xCite1986/esp32_t-display-s3-amoled_ph_meter_pump/firmware/ph_dosieranlage_s3/Settings.cpp

#include "Settings.h"
#include <Preferences.h>

Settings settings;

static Preferences prefs;
static const char *NS = "phdos";

static float clampf(float v, float lo, float hi) {
  if (isnan(v)) return lo;
  return v < lo ? lo : (v > hi ? hi : v);
}

void Settings::clampAll() {
  mlPerSec    = clampf(mlPerSec, HARD_MIN_ML_PER_SEC, HARD_MAX_ML_PER_SEC);
  panelDoseMl = clampf(panelDoseMl, 0.1f, HARD_MAX_SINGLE_DOSE_ML);

  if (standbyS < STANDBY_MIN_S) standbyS = STANDBY_MIN_S;
  if (standbyS > STANDBY_MAX_S) standbyS = STANDBY_MAX_S;
  if (shiftS   < SHIFT_MIN_S)   shiftS   = SHIFT_MIN_S;
  if (shiftS   > SHIFT_MAX_S)   shiftS   = SHIFT_MAX_S;
  if (nightFrom > 23) nightFrom = 20;
  if (nightTo   > 23) nightTo   = 5;

  if (circFreshS   < 10)  circFreshS   = 10;
  if (circFreshS   > 3600) circFreshS  = 3600;
  if (circRetryS   < 15)  circRetryS   = 15;
  if (circRetryS   > 3600) circRetryS  = 3600;
  if (circOffRetryS < 15) circOffRetryS = 15;
  if (circOffRetryS > 3600) circOffRetryS = 3600;
  haHost[sizeof(haHost) - 1]     = 0;
  // Ohne Portangabe landet die Anfrage auf Port 80. Dort laeuft haeufig ein
  // anderer Webserver, der mit 404 antwortet - was wie eine falsche Entitaet
  // aussieht. Home Assistant hoert standardmaessig auf 8123, also ergaenzen.
  if (strlen(haHost) > 0 && strchr(haHost, ':') == nullptr &&
      strlen(haHost) + 5 < sizeof(haHost)) {
    strcat(haHost, ":8123");
  }
  haToken[sizeof(haToken) - 1]   = 0;
  haEntity[sizeof(haEntity) - 1] = 0;
  haOnState[sizeof(haOnState) - 1] = 0;
  if (strlen(haOnState) == 0) strcpy(haOnState, "on");
  // Ohne Adresse, Entitaet oder Token laesst sich nichts pruefen - dann bleibt
  // die Verriegelung aus, statt jede Dosierung zu blockieren.
  if (strlen(haHost) == 0 || strlen(haEntity) == 0 || strlen(haToken) == 0)
    circEnabled = false;

  phSetpoint  = clampf(phSetpoint, 6.0f, 8.5f);
  phDeadband  = clampf(phDeadband, 0.01f, 1.0f);
  phMinLock   = clampf(phMinLock, HARD_MIN_PH_LOCK, 7.5f);
  phMaxPlaus  = clampf(phMaxPlaus, 8.0f, PH_PLAUS_MAX);

  maxSingleMl = clampf(maxSingleMl, 0.1f, HARD_MAX_SINGLE_DOSE_ML);
  doseMl      = clampf(doseMl, 0.1f, maxSingleMl);
  maxDailyMl  = clampf(maxDailyMl, 0.1f, HARD_MAX_DAILY_ML);
  if (pauseS < HARD_MIN_PAUSE_S) pauseS = HARD_MIN_PAUSE_S;
  if (pauseS > 86400UL) pauseS = 86400UL;

  if (adcGain > (uint8_t)ADS_GAIN_0256) adcGain = (uint8_t)ADS_GAIN_4096;
  if (filterS < PH_FILTER_MIN_S) filterS = PH_FILTER_MIN_S;
  if (filterS > PH_FILTER_MAX_S) filterS = PH_FILTER_MAX_S;
  if (phAvgS  < PH_AVG_MIN_S)    phAvgS  = PH_AVG_MIN_S;
  if (phAvgS  > PH_AVG_MAX_S)    phAvgS  = PH_AVG_MAX_S;
  phStableBand = clampf(phStableBand, PH_STABLE_BAND_MIN, PH_STABLE_BAND_MAX);

  calPhA = clampf(calPhA, 0.0f, 14.0f);
  calPhB = clampf(calPhB, 0.0f, 14.0f);
  calVoltA = clampf(calVoltA, -6.2f, 6.2f);
  calVoltB = clampf(calVoltB, -6.2f, 6.2f);
  // Zwei Kalibrierpunkte muessen sich unterscheiden, sonst ist die Gerade sinnlos.
  if (fabsf(calPhA - calPhB) < 0.5f || fabsf(calVoltA - calVoltB) < 0.010f) {
    calValid = false;
  }

  dailyMl = clampf(dailyMl, 0.0f, HARD_MAX_DAILY_ML);
  if (totalMl < 0) totalMl = 0;

  hostname[sizeof(hostname) - 1] = 0;
  wifiSsid[sizeof(wifiSsid) - 1] = 0;
  wifiPass[sizeof(wifiPass) - 1] = 0;
  webUser[sizeof(webUser) - 1]   = 0;
  webPass[sizeof(webPass) - 1]   = 0;
}

static void getStr(Preferences &p, const char *key, char *dst, size_t len, const char *def) {
  String s = p.getString(key, def);
  strncpy(dst, s.c_str(), len - 1);
  dst[len - 1] = 0;
}

void Settings::load() {
  prefs.begin(NS, true);  // read-only

  getStr(prefs, "ssid", wifiSsid, sizeof(wifiSsid), "");
  getStr(prefs, "pass", wifiPass, sizeof(wifiPass), "");
  getStr(prefs, "host", hostname, sizeof(hostname), "ph-dosierung");
  getStr(prefs, "wuser", webUser, sizeof(webUser), "");
  getStr(prefs, "wpass", webPass, sizeof(webPass), "");

  calValid   = prefs.getBool("calok", false);
  calPhA     = prefs.getFloat("cpha", 7.00f);
  calVoltA   = prefs.getFloat("cva", 1.65f);
  calPhB     = prefs.getFloat("cphb", 4.00f);
  calVoltB   = prefs.getFloat("cvb", 2.00f);
  adcGain    = prefs.getUChar("gain", (uint8_t)ADS_GAIN_4096);
  filterS    = (uint16_t)prefs.getULong("filt", 30);
  phAvgS     = (uint16_t)prefs.getULong("avgs", 600);
  phStableBand = prefs.getFloat("stbnd", PH_STABLE_BAND);

  mlPerSec   = prefs.getFloat("mlps", DEFAULT_ML_PER_SEC);
  panelDoseMl= prefs.getFloat("pdose", DEFAULT_PANEL_DOSE_ML);
  relayInvert= prefs.getBool("rinv", false);
  standbyS   = (uint16_t)prefs.getULong("stby", 300);
  shiftS     = (uint16_t)prefs.getULong("shft", 300);
  nightEnabled = prefs.getBool("nite", true);
  rot180     = prefs.getBool("rot180", true);
  nightFrom  = prefs.getUChar("nfrom", 20);
  nightTo    = prefs.getUChar("nto", 5);

  circEnabled = prefs.getBool("circen", false);
  getStr(prefs, "hahost", haHost, sizeof(haHost), "");
  getStr(prefs, "hatok", haToken, sizeof(haToken), "");
  getStr(prefs, "haent", haEntity, sizeof(haEntity), "switch.poolpumpe");
  getStr(prefs, "haon", haOnState, sizeof(haOnState), "on");
  circFreshS  = (uint16_t)prefs.getULong("circfr", 120);
  circRetryS  = (uint16_t)prefs.getULong("circrt", 60);
  circOffRetryS = (uint16_t)prefs.getULong("circof", 120);

  autoEnabled= prefs.getBool("auto", false);
  phSetpoint = prefs.getFloat("sp", 7.20f);
  phDeadband = prefs.getFloat("db", 0.05f);
  doseMl     = prefs.getFloat("dose", 3.00f);
  maxSingleMl= prefs.getFloat("maxs", 5.00f);
  maxDailyMl = prefs.getFloat("maxd", 60.00f);
  pauseS     = prefs.getULong("pause", 1800);
  phMinLock  = prefs.getFloat("phlock", 6.80f);
  phMaxPlaus = prefs.getFloat("phmax", 9.50f);


  dailyMl    = prefs.getFloat("dml", 0.0f);
  dayStamp   = prefs.getULong("dstamp", 0);
  totalMl    = prefs.getFloat("tml", 0.0f);

  prefs.end();
  clampAll();
}

// 95 Prozent der Vollskala: die letzten Prozent gehoeren der Stoerung, die
// auf dem Nutzsignal sitzt. Wird die Spitze abgeschnitten, stimmt auch der
// netzsynchrone Mittelwert nicht mehr.
bool Settings::gainFitsCalibration(uint8_t gainIdx, String &err) const {
  if (gainIdx > (uint8_t)ADS_GAIN_0256) { err = "unbekannter Messbereich"; return false; }
  if (!calValid) return true;                 // ohne Kalibrierung nichts zu pruefen

  float fs   = Ads1115::fullScaleOf((AdsGain)gainIdx) * 0.95f;
  float vmax = fabsf(calVoltA) > fabsf(calVoltB) ? fabsf(calVoltA) : fabsf(calVoltB);
  if (vmax <= fs) return true;

  err  = "Messbereich zu klein: Kalibrierpunkt ";
  err += String(vmax, 3);
  err += " V passt nicht in +/-";
  err += String(Ads1115::fullScaleOf((AdsGain)gainIdx), 3);
  err += " V. Erst Kalibrierung verwerfen, dann umstellen.";
  return false;
}

void Settings::save() {
  clampAll();
  prefs.begin(NS, false);

  prefs.putString("ssid", wifiSsid);
  prefs.putString("pass", wifiPass);
  prefs.putString("host", hostname);
  prefs.putString("wuser", webUser);
  prefs.putString("wpass", webPass);

  prefs.putBool("calok", calValid);
  prefs.putFloat("cpha", calPhA);
  prefs.putFloat("cva", calVoltA);
  prefs.putFloat("cphb", calPhB);
  prefs.putFloat("cvb", calVoltB);
  prefs.putUChar("gain", adcGain);
  prefs.putULong("filt", filterS);
  prefs.putULong("avgs", phAvgS);
  prefs.putFloat("stbnd", phStableBand);

  prefs.putFloat("mlps", mlPerSec);
  prefs.putFloat("pdose", panelDoseMl);
  prefs.putBool("rinv", relayInvert);
  prefs.putULong("stby", standbyS);
  prefs.putULong("shft", shiftS);
  prefs.putBool("nite", nightEnabled);
  prefs.putBool("rot180", rot180);
  prefs.putUChar("nfrom", nightFrom);
  prefs.putUChar("nto", nightTo);

  prefs.putBool("circen", circEnabled);
  prefs.putString("hahost", haHost);
  prefs.putString("hatok", haToken);
  prefs.putString("haent", haEntity);
  prefs.putString("haon", haOnState);
  prefs.putULong("circfr", circFreshS);
  prefs.putULong("circrt", circRetryS);
  prefs.putULong("circof", circOffRetryS);

  prefs.putBool("auto", autoEnabled);
  prefs.putFloat("sp", phSetpoint);
  prefs.putFloat("db", phDeadband);
  prefs.putFloat("dose", doseMl);
  prefs.putFloat("maxs", maxSingleMl);
  prefs.putFloat("maxd", maxDailyMl);
  prefs.putULong("pause", pauseS);
  prefs.putFloat("phlock", phMinLock);
  prefs.putFloat("phmax", phMaxPlaus);


  prefs.putFloat("dml", dailyMl);
  prefs.putULong("dstamp", dayStamp);
  prefs.putFloat("tml", totalMl);

  prefs.end();
}

void Settings::saveCounters() {
  prefs.begin(NS, false);
  prefs.putFloat("dml", dailyMl);
  prefs.putULong("dstamp", dayStamp);
  prefs.putFloat("tml", totalMl);
  prefs.end();
}

void Settings::factoryReset() {
  prefs.begin(NS, false);
  prefs.clear();
  prefs.end();
  *this = Settings();  // Defaults aus der Struktur uebernehmen
  save();
}
